LouDnl/SIDPod-SDCard/src/PSIDCatalog.cpp

#include <cstring>
#include <vector>
#include <cstdio>
#include "PSIDCatalog.h"
#include "platform_config.h"
// custom
#include "hw_config.h"
#include "sd_card.h"
#include "ff.h"
#include "f_util.h"
#include "ff_util.h"

FATFS *fs = new FATFS;
uint32_t PSID_ID = 0x50534944;
std::vector<CatalogEntry> catalog;
std::vector<CatalogEntry *> window;
uint8_t windowPosition = 0;
uint8_t selectedPosition = 0;
uint8_t windowSize = CATALOG_WINDOW_SIZE;

void PSIDCatalog::refresh() {  // BUG: Currently breaks on large quantity of sids ~ out of memory error
    TRACE_PRINTF(">>> %s\n", __FUNCTION__);
    DIR *dp;
    FILINFO fno;
    FRESULT fr;
    dp = new DIR;
    catalog.clear();
    sd_card_t *pSD = sd_get_by_num(0);
    f_mount(&pSD->fatfs, pSD->pcName, 1);
    f_opendir(dp, "");
    while (true) {
        fr = f_readdir(dp, &fno);
        if (fr != FR_OK || fno.fname[0] == 0) break;
        if (isRegularFile(&fno)) {
            tryToAddAsPsid(&fno);  // TODO: Change this to just load the filenames
        }
    }
    f_closedir(dp);
    delete dp;
    resetAccessors();
}

CatalogEntry *PSIDCatalog::getCurrentEntry() {
    return &catalog.at(selectedPosition);
}

size_t PSIDCatalog::getSize() {
    return catalog.size();
}

std::vector<CatalogEntry *> PSIDCatalog::getWindow() {
    return window;
}

void PSIDCatalog::selectNext() {
    if (selectedPosition < getSize() - 1) {
        selectedPosition++;
        slideDown();
        updateWindow();
    }
}

void PSIDCatalog::selectPrevious() {
    if (selectedPosition > 0) {
        selectedPosition--;
        slideUp();
        updateWindow();
    }
}

void PSIDCatalog::resetAccessors() {
    selectedPosition = 0;
    windowPosition = 0;
    if (getSize() > 0) {
        updateWindow();
    }
}

void PSIDCatalog::tryToAddAsPsid(FILINFO *fileInfo) {
    FIL pFile;
    BYTE header[PSID_MINIMAL_HEADER_SIZE];
    UINT bytesRead;
    f_open(&pFile, fileInfo->altname, FA_READ);
    f_read(&pFile, &header, PSID_MINIMAL_HEADER_SIZE, &bytesRead);
    if (bytesRead == PSID_MINIMAL_HEADER_SIZE) {
        uint32_t magic = header[3] | (header[2] << 0x08) | (header[1] << 0x10) | (header[0] << 0x18);
        if (magic == PSID_ID) {
            auto *pHeader = (unsigned char *) header;
            CatalogEntry entry{};
            entry.unplayable = false;
            strcpy(entry.fileName, fileInfo->altname);
            strcpy(entry.title, (const char *) &pHeader[0x16]);
            catalog.push_back(entry);
        }
    }
    f_close(&pFile);
}


void PSIDCatalog::slideDown() {
    if (windowSize + windowPosition < getSize()) {
        windowPosition++;
    }
}

void PSIDCatalog::slideUp() {
    if (windowPosition > 0) {
        windowPosition--;
    }
}

void PSIDCatalog::updateWindow() {
    if (getSize()) {
        window.clear();
        for (int i = 0; i < std::min(windowSize, (uint8_t) getSize()); i++) {
            auto entry = &catalog.at(windowPosition + i);
            entry->selected = windowPosition + i == selectedPosition;
            window.push_back(entry);
        }
    }
}

bool PSIDCatalog::isRegularFile(FILINFO *fileInfo) {
    return fileInfo->fattrib == 32 && fileInfo->fname[0] != 46;
}

void PSIDCatalog::markCurrentEntryAsUnplayable() {
    getCurrentEntry()->unplayable = true;
}
