LouDnl/SIDPod-SDCard/include/sidpod_bmp.h

const unsigned char SIDPOD_BMP[] = { 
0x42, 0x4d, 0x82, 0x02, 0x00, 0x00, 0x00, 0x00, 0x00, 0x00, 0x82, 0x00, 0x00, 0x00, 0x6c, 0x00, 
0x00, 0x00, 0x80, 0x00, 0x00, 0x00, 0x20, 0x00, 0x00, 0x00, 0x01, 0x00, 0x01, 0x00, 0x00, 0x00, 
0x00, 0x00, 0x00, 0x02, 0x00, 0x00, 0x00, 0x00, 0x00, 0x00, 0x00, 0x00, 0x00, 0x00, 0x02, 0x00, 
0x00, 0x00, 0x02, 0x00, 0x00, 0x00, 0x00, 0x00, 0xff, 0x00, 0x00, 0xff, 0x00, 0x00, 0xff, 0x00, 
0x00, 0x00, 0x00, 0x00, 0x00, 0xff, 0x42, 0x47, 0x52, 0x73, 0x00, 0x00, 0x00, 0x00, 0x00, 0x00, 
0x00, 0x00, 0x00, 0x00, 0x00, 0x40, 0x00, 0x00, 0x00, 0x00, 0x00, 0x00, 0x00, 0x00, 0x00, 0x00, 
0x00, 0x40, 0x00, 0x00, 0x00, 0x00, 0x00, 0x00, 0x00, 0x00, 0x00, 0x00, 0x00, 0x40, 0x00, 0x00, 
0x00, 0x00, 0x00, 0x00, 0x00, 0x00, 0x00, 0x00, 0x00, 0x00, 0x00, 0x00, 0x00, 0x00, 0xff, 0xff, 
0xff, 0x00, 0x00, 0x00, 0x00, 0x7f, 0xc1, 0xe0, 0x00, 0x3f, 0xc1, 0xff, 0xff, 0xf0, 0x00, 0x7f, 
0x00, 0x07, 0x00, 0x00, 0x00, 0x1f, 0xc1, 0xc0, 0x00, 0x0f, 0xc1, 0xff, 0xff, 0xe0, 0x00, 0x3e, 
0x00, 0x03, 0x00, 0x00, 0x00, 0x07, 0xc1, 0xc0, 0x00, 0x07, 0xc1, 0xff, 0xff, 0xc0, 0x00, 0x1c, 
0x00, 0x01, 0x00, 0x00, 0x00, 0x03, 0xc1, 0xc0, 0x00, 0x03, 0xc1, 0xff, 0xff, 0x80, 0x00, 0x1c, 
0x00, 0x00, 0x00, 0x00, 0x00, 0x03, 0xc1, 0xc0, 0x00, 0x01, 0xc1, 0xff, 0xff, 0x80, 0x00, 0x08, 
0x00, 0x00, 0x00, 0x00, 0x00, 0x01, 0xc1, 0xc1, 0xff, 0x81, 0xc0, 0x00, 0x1f, 0x83, 0xfe, 0x08, 
0x3f, 0xe0, 0x00, 0x00, 0x00, 0x01, 0xc1, 0xc1, 0xff, 0xc0, 0xc0, 0x00, 0x07, 0x83, 0xfe, 0x08, 
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
0xff, 0xff, 0xf0, 0x00, 0x00, 0x07, 0xc0, 0xff, 0xff, 0xff, 0xff, 0xff, 0xff, 0xff, 0xff, 0xff, 
0xff, 0xff, 0xfc, 0x00, 0x00, 0x07, 0xe1, 0xff, 0xff, 0xff, 0xff, 0xff, 0xff, 0xff, 0xff, 0xff, 
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

const size_t SIDPOD_BMP_SIZE = 642;
